MOSH-Insa-Toulouse/2024-2025-4GP-MelissandE46-SofiaManzueta/Application Android/Code_Mesures.PNG

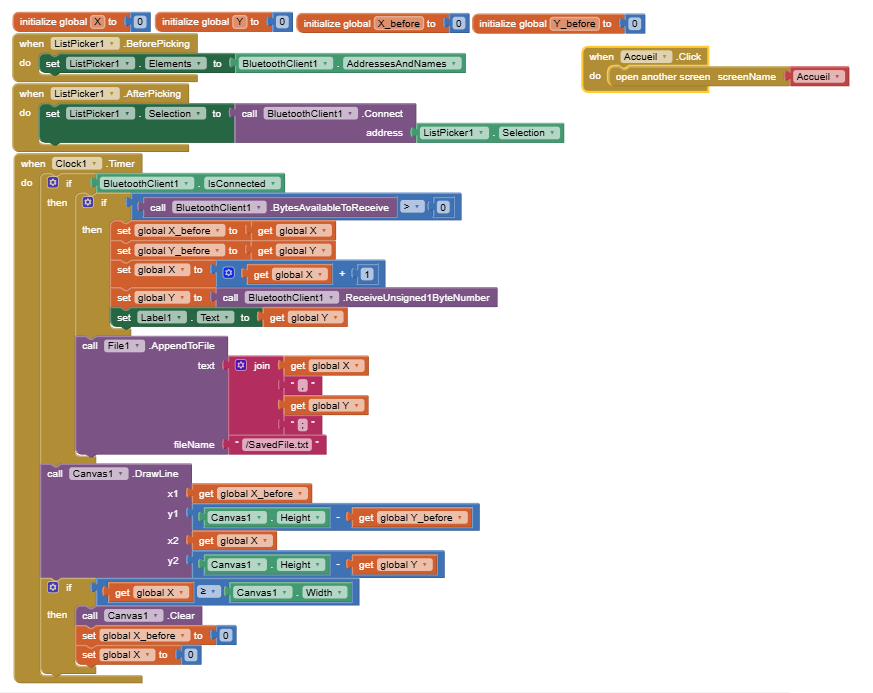
Application Android/Code_Mesures.PNG
