MOSH-Insa-Toulouse/2024-2025-4GP-MelissandE46-SofiaManzueta/Application Android/Face avant_Informations.PNG

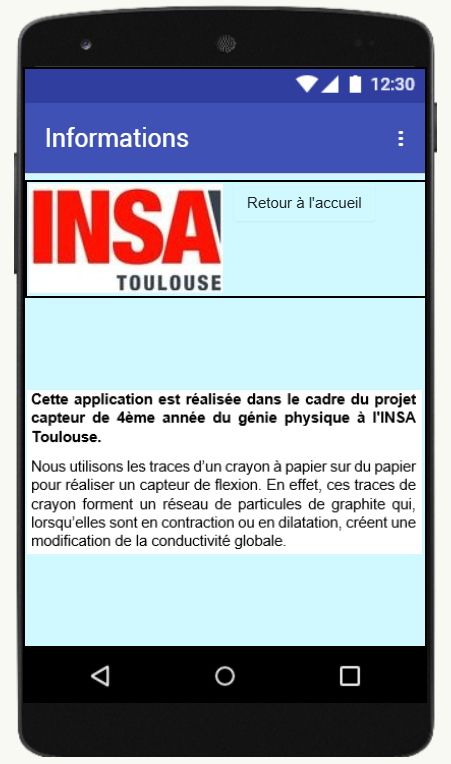
Application Android/Face avant_Informations.PNG
