MOSH-Insa-Toulouse/2024-2025-4GP-MelissandE46-SofiaManzueta/Application Android/Face avant_Mesures.PNG

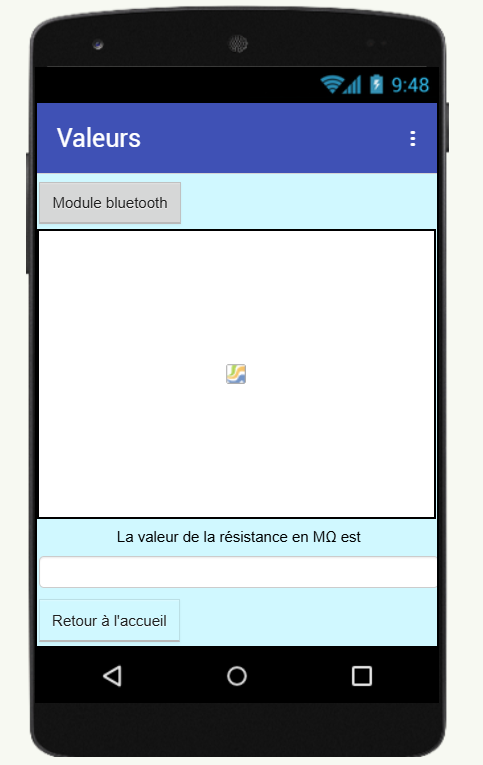
Application Android/Face avant_Mesures.PNG
