MOSH-Insa-Toulouse/2024-2025-4GP-MelissandE46-SofiaManzueta/Kidad - Projet capteur/Modèle 3D.png

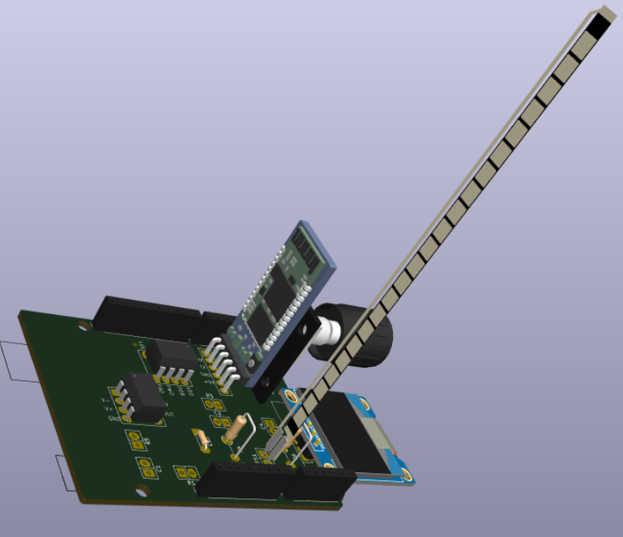
Kidad - Projet capteur/Modèle 3D.png
