MOSH-Insa-Toulouse/2024-2025-4GP-MelissandE46-SofiaManzueta/Kidad - Projet capteur/PCB finale.jpg

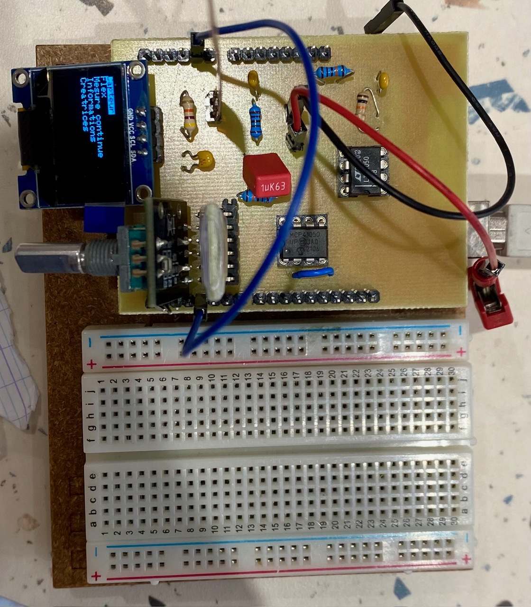
Kidad - Projet capteur/PCB finale.jpg
