MOSH-Insa-Toulouse/2024-2025-4GP-MelissandE46-SofiaManzueta/Kidad - Projet capteur/Rooting PCB.png

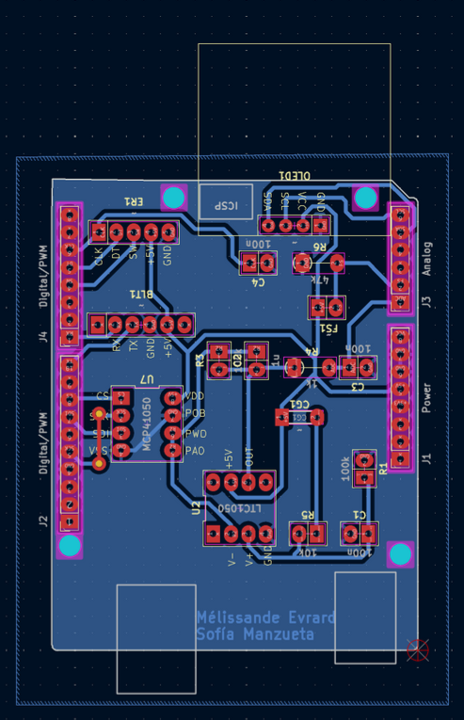
Kidad - Projet capteur/Rooting PCB.png
