MOSH-Insa-Toulouse/2024-2025-4GP-MelissandE46-SofiaManzueta/Mesures/Variation résistance flex sensor tension.PNG

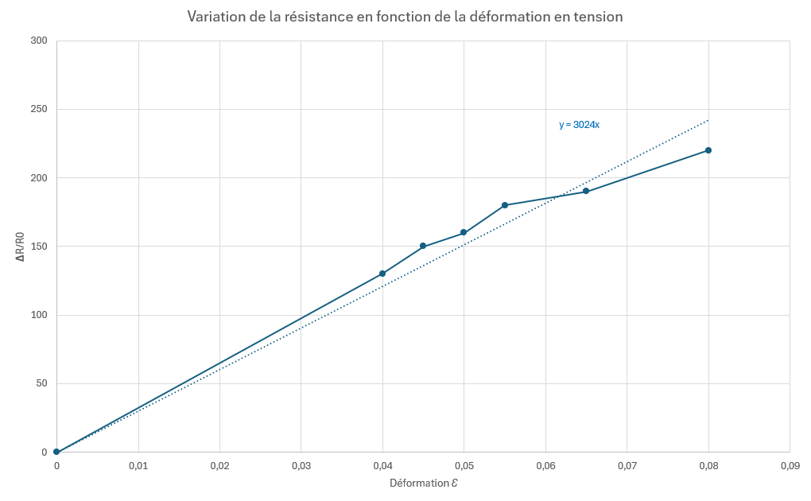
Mesures/Variation résistance flex sensor tension.PNG
