MOSH-Insa-Toulouse/2024-2025-4GP-MelissandE46-SofiaManzueta/TPCapteursLTSpice/SimulationLTSpice.PNG

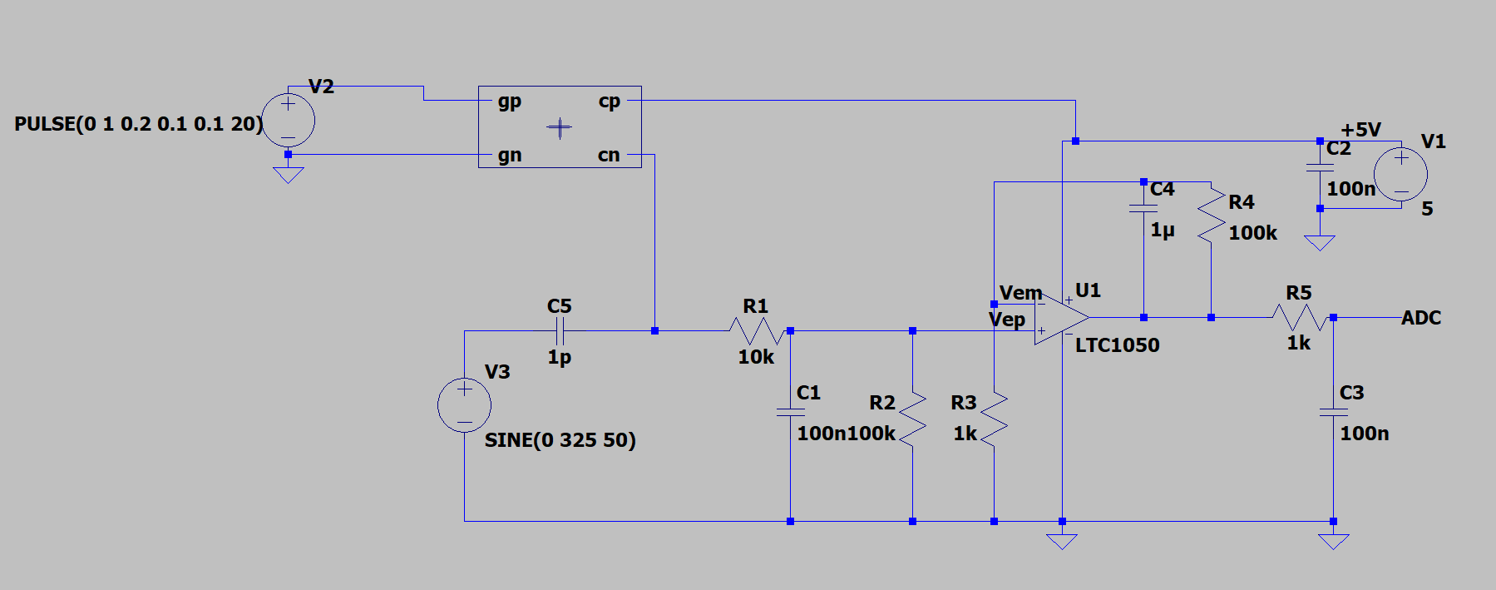
TPCapteursLTSpice/SimulationLTSpice.PNG
