MOSH-Insa-Toulouse/2024-2025-4GP-MelissandE46-SofiaManzueta/TPCapteursLTSpice/Modelcapteur.asc

B1: bi; I=V(cp,cn)*(10n+10n*V(gc,gn))
C1: cap; 200µ
R1: res; 1k
Named nets: cp, cn, gp, gn, gc
