MOSH-Insa-Toulouse/2024-2025-4GP-MelissandE46-SofiaManzueta/TPCapteursLTSpice/TP1Capteur.asc

C1: cap; 100n
C2: cap; 100n
C3: cap; 100n
C4: cap; 1µ
C5: cap; 1p
R1: res; 10k
R2: res; 100k
R3: res; 1k
R4: res; 100k
R5: res; 1k
U1: LTC1050
V1: voltage; 5
V2: voltage; PULSE(0 1 0.2 0.1 0.1 20)
V3: voltage; SINE(0 325 50)
X1: Modelcapteur
Named nets: 0, ADC, Vem, Vep, +5V
.tran 2
;ac dec 100 1 1G
