MOSH-Insa-Toulouse/2024-2025-4GP-MelissandE46-SofiaManzueta/TPCapteursLTSpice/TP4Elec2.asc

C1: cap; 220n
C2: cap; 47n
C3: cap; 47µ
C4: cap; 1µ
C5: cap; 100µ
C6: cap; 20n
C7: cap; 20n
C8: cap; 100p
J1: njf; 2N4416
Q1: npn; BC547B
Q2: npn; 2N2222
R1: res; 1.5k
R2: res; 100k
R3: res; 4.7
R4: res; 220
R5: res; 68k
R6: res; 560k
R7: res; 4.7k
R8: res; 1k
R9: res; 220k
R10: res; 220k
R11: res; 390
R12: res; 1.5k
R13: res; 390
R14: res; 47
R15: res; 120k
R16: res; 4.7
R17: res; 2.4
R18: res; 80.6k
R19: res; 4.7k
U1: OP27
V1: signal; SINE(0 140u 10K); AC 140u 0
V2: voltage; 15
V3: voltage; -15
Named nets: 0, entree, sortie, out, -V, +V, filtre_out, op27_out
;.ac dec 1000 10 10meg
.noise V(filtre_out) V1 dec 1000 10 1meg
